matthewlai/ESP32LEDControl/hardware/esp32_led_controller/doc/rev4_hw_qual/cable2_led_on.png

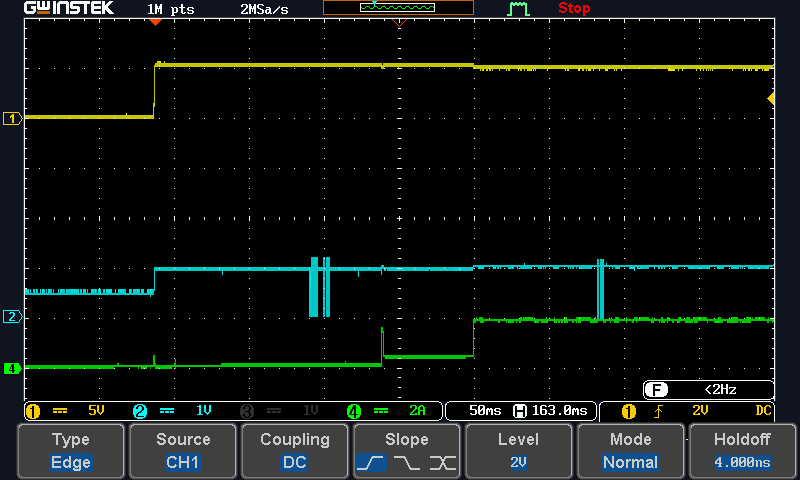
hardware/esp32_led_controller/doc/rev4_hw_qual/cable2_led_on.png
