matthewlai/ESP32LEDControl/hardware/esp32_led_controller/doc/rev4_hw_qual/dout_stats.png

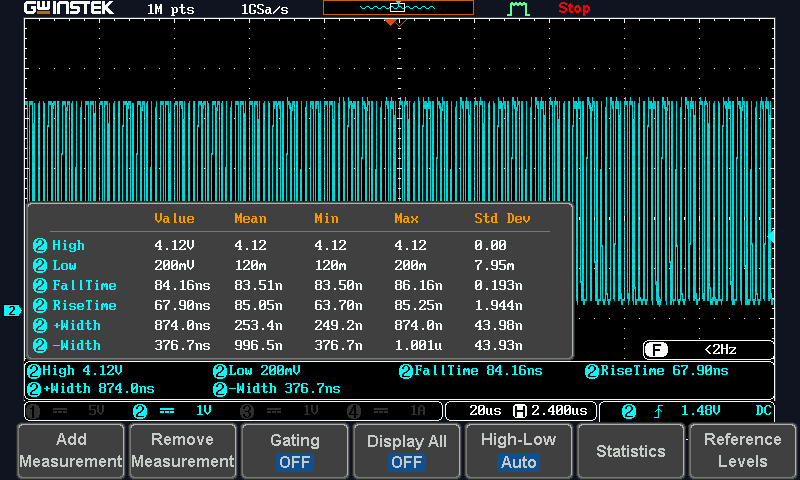
hardware/esp32_led_controller/doc/rev4_hw_qual/dout_stats.png
